RubenHaag/Jufo_Bikelight/Arbeit/P3.png

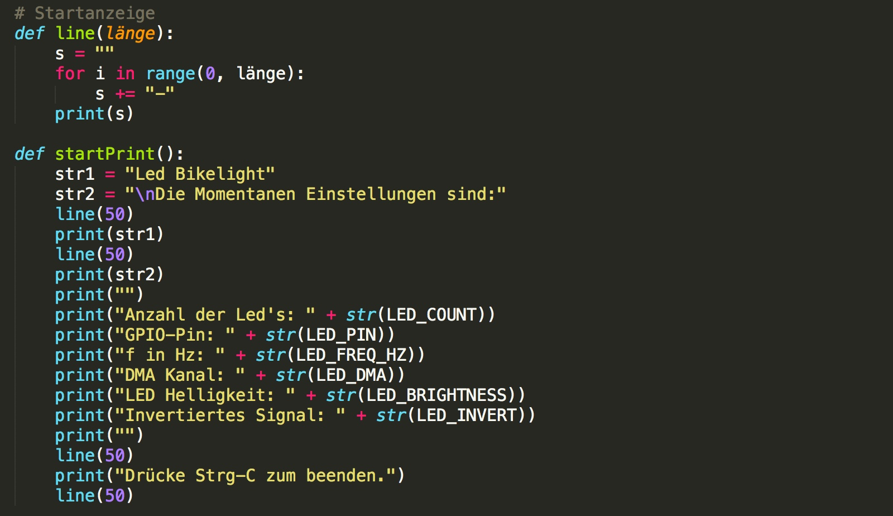
Arbeit/P3.png
