RubenHaag/Jufo_Bikelight/Website/Bild/a10d65f4-1c05-486a-bddb-3542008c965d.jpg

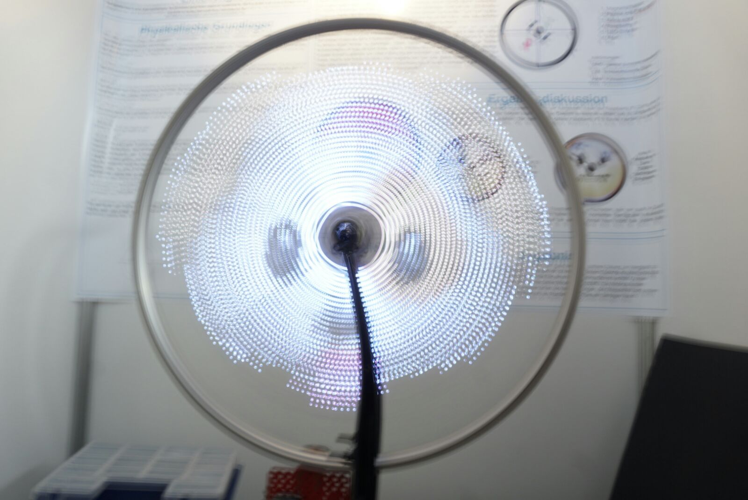
Website/Bild/a10d65f4-1c05-486a-bddb-3542008c965d.jpg
