RubenHaag/Jufo_Bikelight/Website/Bild/Materialkosten_Tabelle.png

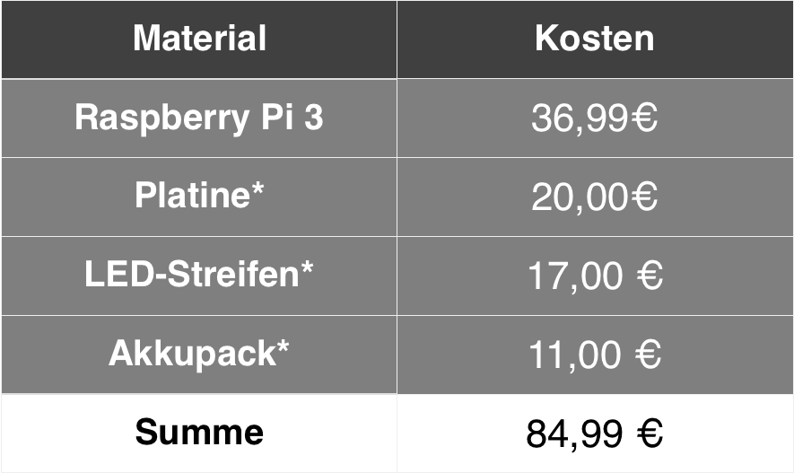
Website/Bild/Materialkosten_Tabelle.png
